Tinymaxi/NewKorndispenser/drivers/buzzer/Buzzer.cpp

#include "Buzzer.hpp"

#include "pico/stdlib.h"
#include "hardware/pwm.h"
#include "hardware/clocks.h"
#include <algorithm>
#include <cmath>

// Clamp helper
static inline float clamp01(float v) { return v < 0.f ? 0.f : (v > 1.f ? 1.f : v); }

Buzzer::Buzzer(int gpio_buzzer)
: _gpio(gpio_buzzer)
{
    gpio_set_function(_gpio, GPIO_FUNC_PWM);
    _slice   = pwm_gpio_to_slice_num(_gpio);
    _channel = pwm_gpio_to_channel(_gpio);

    pwm_config cfg = pwm_get_default_config();
    pwm_config_set_clkdiv(&cfg, 1.0f);
    pwm_init(_slice, &cfg, true);

    pwm_set_gpio_level(_gpio, 0); // silent start
}

void Buzzer::startTone(uint32_t freq_hz, float volume)
{
    volume = clamp01(volume);

    if (freq_hz == 0) {
        stopTone();
        return;
    }

    const double clk = (double)clock_get_hz(clk_sys);

    // pick divider so TOP fits in 16-bit
    double div_d = ceil(clk / ((double)freq_hz * 65536.0));
    if (div_d < 1.0) div_d = 1.0;
    if (div_d > 255.0) div_d = 255.0;

    double top_d = (clk / (div_d * (double)freq_hz)) - 1.0;

    // improve resolution if top is too small
    if (top_d < 200.0 && div_d < 255.0) {
        double div_target = ceil(clk / ((double)freq_hz * 400.0));
        if (div_target >= 1.0 && div_target <= 255.0) {
            div_d = div_target;
            top_d = (clk / (div_d * (double)freq_hz)) - 1.0;
        }
    }

    if (top_d > 65535.0) top_d = 65535.0;
    if (top_d < 1.0)     top_d = 1.0;

    uint16_t top = (uint16_t)llround(top_d);
    pwm_set_clkdiv(_slice, (float)div_d);
    pwm_set_wrap(_slice, top);

    uint16_t level = (uint16_t)(((uint32_t)top + 1u) * 0.5f * volume);
    pwm_set_chan_level(_slice, _channel, level);
    pwm_set_enabled(_slice, true);
}

void Buzzer::stopTone()
{
    pwm_set_chan_level(_slice, _channel, 0);
    pwm_set_enabled(_slice, true);
}

void Buzzer::playTone(uint32_t freq_hz, uint32_t duration_ms, float volume)
{
    startTone(freq_hz, volume);
    sleep_ms(duration_ms);
    stopTone();
}

void Buzzer::rest(uint32_t duration_ms)
{
    stopTone();
    sleep_ms(duration_ms);
}

void Buzzer::beep(uint32_t duration_ms, float volume)
{
    const uint32_t f1 = 1400, f2 = 1800;
    playTone(f1, duration_ms, volume);
    rest(duration_ms / 3);
    playTone(f2, duration_ms, volume);
}

void Buzzer::playMelody(const std::vector<Note>& melody, uint32_t gap_ms, float volume)
{
    for (auto& n : melody) {
        if (n.freq_hz == 0) rest(n.duration_ms);
        else playTone(n.freq_hz, n.duration_ms, volume);
        if (gap_ms) rest(gap_ms);
    }
}

// --- Note frequencies ---
namespace {
constexpr uint32_t NOTE_C3=130,  NOTE_D3=146,  NOTE_E3=164,  NOTE_F3=174,
                   NOTE_G3=196,  NOTE_A3=220,  NOTE_B3=246;
constexpr uint32_t NOTE_C4=261,  NOTE_D4=293,  NOTE_E4=329,  NOTE_F4=349,
                   NOTE_G4=392,  NOTE_A4=440,  NOTE_B4=493;
constexpr uint32_t NOTE_C5=523,  NOTE_D5=587,  NOTE_E5=659,  NOTE_F5=698,
                   NOTE_G5=784,  NOTE_A5=880,  NOTE_B5=987;
constexpr uint32_t NOTE_C6=1046, NOTE_D6=1174, NOTE_E6=1318, NOTE_F6=1396,
                   NOTE_G6=1567, NOTE_A6=1760, NOTE_B6=1975;

static inline uint32_t dur_quarter(uint32_t bpm) {
    return 60000u / std::max<uint32_t>(bpm, 1);
}
}

std::vector<Buzzer::Note> Buzzer::melodyOdeToJoy(uint32_t tempo_bpm)
{
    const uint32_t q = dur_quarter(tempo_bpm);
    const uint32_t h = 2*q;
    const uint32_t e = q/2;

    return {
        {NOTE_E4, q}, {NOTE_E4, q}, {NOTE_F4, q}, {NOTE_G4, q},
        {NOTE_G4, q}, {NOTE_F4, q}, {NOTE_E4, q}, {NOTE_D4, q},
        {NOTE_C4, q}, {NOTE_C4, q}, {NOTE_D4, q}, {NOTE_E4, q},
        {NOTE_E4, e}, {NOTE_D4, e}, {NOTE_D4, h},
        {NOTE_E4, q}, {NOTE_E4, q}, {NOTE_F4, q}, {NOTE_G4, q},
        {NOTE_G4, q}, {NOTE_F4, q}, {NOTE_E4, q}, {NOTE_D4, q},
        {NOTE_C4, q}, {NOTE_C4, q}, {NOTE_D4, q}, {NOTE_E4, q},
        {NOTE_D4, q}, {NOTE_C4, q}, {NOTE_C4, h}
    };
}

std::vector<Buzzer::Note> Buzzer::melodyTwinkle(uint32_t tempo_bpm)
{
    const uint32_t q = dur_quarter(tempo_bpm);
    const uint32_t h = 2*q;

    return {
        {NOTE_C4, q}, {NOTE_C4, q}, {NOTE_G4, q}, {NOTE_G4, q},
        {NOTE_A4, q}, {NOTE_A4, q}, {NOTE_G4, h},
        {NOTE_F4, q}, {NOTE_F4, q}, {NOTE_E4, q}, {NOTE_E4, q},
        {NOTE_D4, q}, {NOTE_D4, q}, {NOTE_C4, h},
        {NOTE_G4, q}, {NOTE_G4, q}, {NOTE_F4, q}, {NOTE_F4, q},
        {NOTE_E4, q}, {NOTE_E4, q}, {NOTE_D4, h},
        {NOTE_G4, q}, {NOTE_G4, q}, {NOTE_F4, q}, {NOTE_F4, q},
        {NOTE_E4, q}, {NOTE_E4, q}, {NOTE_D4, h},
        {NOTE_C4, q}, {NOTE_C4, q}, {NOTE_G4, q}, {NOTE_G4, q},
        {NOTE_A4, q}, {NOTE_A4, q}, {NOTE_G4, h},
        {NOTE_F4, q}, {NOTE_F4, q}, {NOTE_E4, q}, {NOTE_E4, q},
        {NOTE_D4, q}, {NOTE_D4, q}, {NOTE_C4, h}
    };
}

// --- Special Sound Effects ---

void Buzzer::playMacStartup(float volume)
{
    // Mac-like startup chime - warm ascending arpeggio with sustained feel
    // F#maj chord approximation: F#, A#, C#, F# (octave up)
    // Using close frequencies for a pleasing "tech startup" sound
    const uint32_t FS4 = 370;   // F#4
    const uint32_t AS4 = 466;   // A#4
    const uint32_t CS5 = 554;   // C#5
    const uint32_t FS5 = 740;   // F#5

    // Quick arpeggio then hold the high note
    playTone(FS4, 80, volume);
    playTone(AS4, 80, volume);
    playTone(CS5, 80, volume);
    playTone(FS5, 400, volume);  // Hold the top note
    rest(50);
}

void Buzzer::playCloseEncounters(float volume)
{
    // The famous 5-note alien sequence from Close Encounters
    // Notes: G, A, F, F(octave down), C
    // Iconic "communication" melody
    const uint32_t dur = 280;  // Each note duration
    const uint32_t gap = 60;   // Gap between notes

    playTone(NOTE_G4, dur, volume);
    rest(gap);
    playTone(NOTE_A4, dur, volume);
    rest(gap);
    playTone(NOTE_F4, dur, volume);
    rest(gap);
    playTone(NOTE_F3, dur, volume);  // Octave drop!
    rest(gap);
    playTone(NOTE_C4, dur + 200, volume);  // Hold the last note longer
    rest(100);
}

void Buzzer::playMarioCoin(float volume)
{
    // Classic Mario coin "bling!" - two quick high notes
    // B5 -> E6, very snappy
    playTone(NOTE_B5, 60, volume);
    playTone(NOTE_E6, 180, volume);
}

void Buzzer::playDasBoot(float volume)
{
    // Das Boot theme by Klaus Doldinger - the iconic synth melody
    // Key of E minor, slow dramatic tempo (~108 BPM)
    const uint32_t NOTE_E4 = 329;
    const uint32_t NOTE_FS4 = 370;  // F#4
    const uint32_t NOTE_D4 = 293;
    const uint32_t NOTE_B3 = 246;
    const uint32_t NOTE_E3 = 164;

    const uint32_t s = 220;   // Short note (eighth)
    const uint32_t m = 350;   // Medium note (quarter)
    const uint32_t l = 500;   // Long note (held)
    const uint32_t g = 80;    // Gap between notes

    // The iconic opening motif: E-E-E-D-E-F#-E (slow and dramatic)
    playTone(NOTE_E4, s, volume); rest(g);
    playTone(NOTE_E4, s, volume); rest(g);
    playTone(NOTE_E4, s, volume); rest(g);
    playTone(NOTE_D4, s, volume); rest(g);
    playTone(NOTE_E4, m, volume); rest(g);
    playTone(NOTE_FS4, m, volume); rest(g);
    playTone(NOTE_E4, l, volume); rest(g);

    // Descending bass response
    playTone(NOTE_B3, m, volume); rest(g);
    playTone(NOTE_E3, l + 200, volume);  // Hold the final low E
}
